rjrouquette/radio_astronomy/ltspice/micro_filter.asc

I1: current; ""; AC 1
R1: res; 50
R4: res; 50
T1: tline; Td=0.177n Z0=165.6
T2: tline; Td=0.177n Z0=9.6
T3: tline; Td=0.177n Z0=165.6
T4: tline; Td=0.177n Z0=17.6
T5: tline; Td=0.177n Z0=7.6
T6: tline; Td=0.177n Z0=165.6
T7: tline; Td=0.177n Z0=9.6
T8: tline; Td=0.177n Z0=165.6
T9: tline; Td=0.177n Z0=17.6
T10: tline; Td=0.177n Z0=90.8
T11: tline; Td=0.177n Z0=90.8
Named nets: 0
.ac lin 20000 1Meg 3000Meg
