rjrouquette/radio_astronomy/ltspice/slave_clock.asc

A1: xor; Vhigh=3.3 Ref=1.65 td=4.4ns
A2: dflop; Vhigh=3.3 Ref=1.65 td=5.5ns
A3: inv; Vhigh=3.3 Ref=1.65 td=4.4ns
A4: inv; Vhigh=3.3 Ref=1.65 td=4.4ns
A5: xor; Vhigh=3.3 Ref=1.65 td=4.4ns
A6: xor; Vhigh=3.3 Ref=1.65 td=4.4ns
A7: modulate; mark=25.00125Meg space=24.99875Meg
A8: inv; Vhigh=3.3 Ref=1.65 td=4.4ns
A9: inv; Vhigh=3.3 Ref=1.65 td=4.4ns
A11: dflop; Vhigh=3.3 Ref=1.65 td=5.5ns
A12: xor; Vhigh=3.3 Ref=1.65 td=4.4ns
A13: inv; Vhigh=3.3 Ref=1.65 td=4.4ns
A16: inv; Vhigh=3.3 Ref=1.65 td=4.4ns
C1: cap; 100n
C2: cap; 100n
C3: cap; 1n
C4: cap; 10n
C5: cap; 10n
C6: cap; 100n
C7: cap; 330p
C10: cap; 1n
D1: diode; 1N914
R1: res; 1k
R2: res; 66k
R3: res; 66k
R4: res; 3.3k
R5: res; 69k
R6: res; 1k
R7: res; 47k
R10: res; 30k
R11: res; 33k
R12: res; 50
R13: res; 50
R16: res; 330
T1: tline
V1: voltage; 1.65
V2: voltage; PULSE(0 3.3 0 2n 2n 18n 40.000n)
V3: voltage; PULSE(0 3.3 2m 2n 2n 100u 1m)
V4: voltage; 3.3
Named nets: 0, pps, fb, clk
.tran 100m
