rjrouquette/radio_astronomy/ltspice/gpsdo_lowpass.asc

C1: cap; 1µ
C2: cap; 330n
C3: cap; 100n
R1: res; 330
R2: res; 1k
R3: res; 3.3k
R4: res; 100k
V1: voltage; ""; AC 1; Rser=1k
Named nets: 0, out
.ac oct 100 1m 100Meg
