rjrouquette/radio_astronomy/ltspice/poe.asc

C1: cap; 1000µ
C2: cap; 10µ
C4: cap; 200n
C5: cap; 100p
C6: cap; 100p
D1: schottky; RBR10BM30A
D2: zener; 1N750
D3: zener; BZX84C12L
D4: schottky; RBR10BM30A
D5: schottky; RBR10BM30A
D6: schottky; RBR10BM30A
L1: ind2; 19.12µ; Rser=1.03
L2: ind2; 235n; Rser=115m
M1: nmos; IPD530N15N3
Q1: pnp; 2N3906
Q2: pnp; 2N3906
R1: res; 1k
R2: res; 27k
R3: res; 1.5k
R4: res; 13k
R5: res; 330
R6: res; 4.7k
R7: res; 1.25
R8: res; 4.3k
R9: res; 820
U1: NE555
U2: 4N25
U3: NE555
V1: voltage; 56; Rser=10
Named nets: 0, out, REF, FB
K1 L1 L2 0.999
.tran 20m startup
.temp 40
4x Wurth 749196141
