rjrouquette/radio_astronomy/ltspice/ltc5566_matching_374MHz.asc

C1: cap; 18p
C2: cap; 10n
I1: current; ""; AC 1
L1: ind; 1.8n
L2: ind; 11n
R1: res; 9.9
R2: res; 50
Named nets: 0, IN, OUT
.ac oct 1000 10Meg 1000Meg
