rjrouquette/radio_astronomy/analysis/frequency/butter.h

//
// Created by robert on 6/4/20.
//

#ifndef FREQUENCY_RESPONSE_BUTTER_H
#define FREQUENCY_RESPONSE_BUTTER_H

// butterworth band-pass filter
class butter {

};


#endif //FREQUENCY_RESPONSE_BUTTER_H
